FlynnStudios/modular-mealworm-habitat/doc/images/c_joint_selected_assembled.jpg

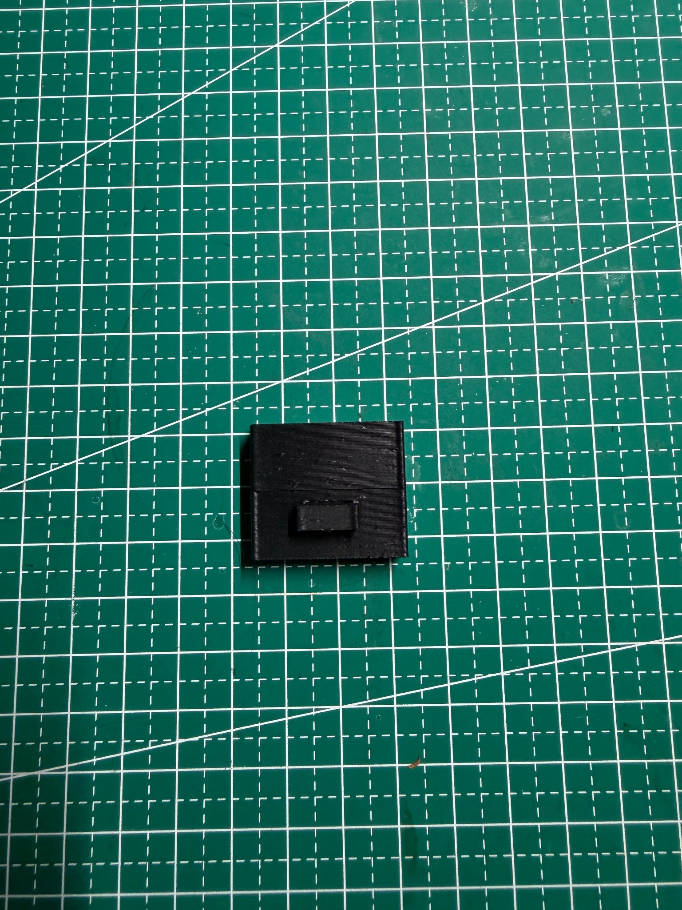
doc/images/c_joint_selected_assembled.jpg
