FlynnStudios/modular-mealworm-habitat/doc/images/rack_tier_print_plate.jpg

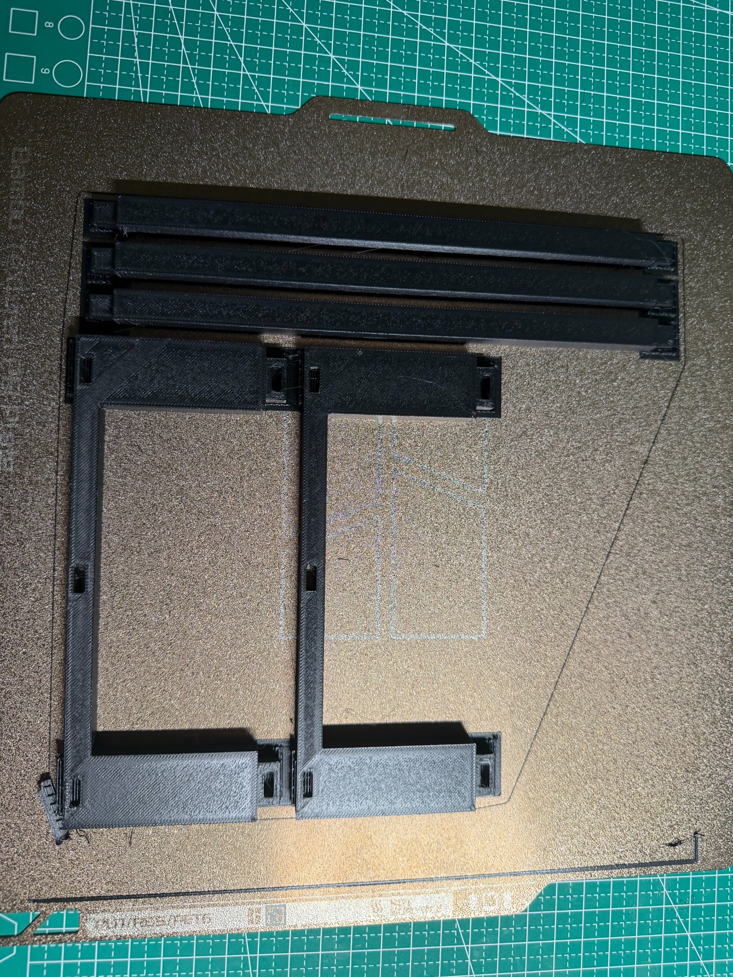
doc/images/rack_tier_print_plate.jpg
