FlynnStudios/modular-mealworm-habitat/doc/images/six_vent_print_plate.jpg

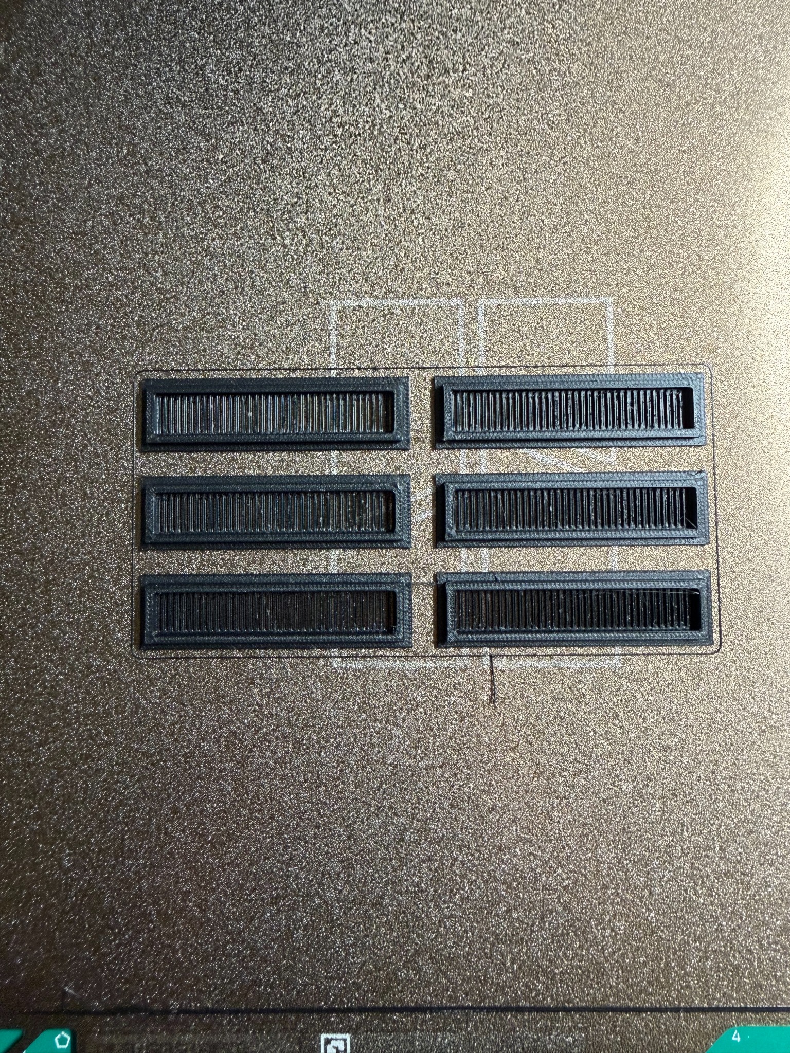
doc/images/six_vent_print_plate.jpg
